fractalclockwork/core-memory/kicad/core_element_sim/models/array64x64_cycle_tb.cir

* Diagonal addressing smoke on the NxN MCE weave.
* Pin order matches magnetic_core_64x64.kicad_sch after Sim.Pins.
* Lines are 0-based: X0/Y0, X1/Y1, ... X63/Y63. There is no X64.
* This deck pulses X0/Y0 through X31/Y31.
*
* One CCS each for X, Y, and inhibit, 400 mA. Inhibit stays off.
* Each pulsed core gets one write 1 (1 us rise, 2 us flat, 1 us fall).
* The diagonal and one X half-select neighbor per address are the mce
* devices. Other positions are omitted; each driven line still
* series-connects the cores that sit on it. Sense is the early flat.
*
* Batch: kicad/core_element_sim/models/array64x64_cycle.sh
* Prints RESULT PASS or RESULT FAIL.

.include coremem.cir
.include ccs.cir

.param vdrive=12

Vdrive vdrv 0 DC {vdrive}
Viccsx ccs_x ccs_xin 0
Viccsy ccs_y ccs_yin 0
Viccsi ccs_i ccs_iin 0
Xccs_x ccs_xin ccs ic_half=0.4
Xccs_y ccs_yin ccs ic_half=0.4
Xccs_i ccs_iin ccs ic_half=0.4
Rx ccs_x 0 10Meg
Ry ccs_y 0 10Meg
Ri ccs_i 0 10Meg
Rfold FOLD 0 10k

Rxa0 xa0d 0 10Meg
Rya0 ya0d 0 10Meg
Rxa1 xa1d 0 10Meg
Rya1 ya1d 0 10Meg
Rxa2 xa2d 0 10Meg
Rya2 ya2d 0 10Meg
Rxa3 xa3d 0 10Meg
Rya3 ya3d 0 10Meg
Rxa4 xa4d 0 10Meg
Rya4 ya4d 0 10Meg
Rxa5 xa5d 0 10Meg
Rya5 ya5d 0 10Meg
Rxa6 xa6d 0 10Meg
Rya6 ya6d 0 10Meg
Rxa7 xa7d 0 10Meg
Rya7 ya7d 0 10Meg
Rxa8 xa8d 0 10Meg
Rya8 ya8d 0 10Meg
Rxa9 xa9d 0 10Meg
Rya9 ya9d 0 10Meg
Rxa10 xa10d 0 10Meg
Rya10 ya10d 0 10Meg
Rxa11 xa11d 0 10Meg
Rya11 ya11d 0 10Meg
Rxa12 xa12d 0 10Meg
Rya12 ya12d 0 10Meg
Rxa13 xa13d 0 10Meg
Rya13 ya13d 0 10Meg
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
Xr48c47 nx47_47 XB47 ny47_48 YB48 nyb47 nyb46 mce m0=-1
Xr48c48 XA48 nx48_48 YA48 ny47_48 nya15 nya14 mce m0=-1
Xr49c48 nx48_48 XB48 ny48_49 YB49 nyb48 nyb47 mce m0=-1
Xr49c49 XA49 nx49_49 YA49 ny48_49 nya14 nya13 mce m0=-1
Xr50c49 nx49_49 XB49 ny49_50 YB50 nyb49 nyb48 mce m0=-1
Xr50c50 XA50 nx50_50 YA50 ny49_50 nya13 nya12 mce m0=-1
Xr51c50 nx50_50 XB50 ny50_51 YB51 nyb50 nyb49 mce m0=-1
Xr51c51 XA51 nx51_51 YA51 ny50_51 nya12 nya11 mce m0=-1
Xr52c51 nx51_51 XB51 ny51_52 YB52 nyb51 nyb50 mce m0=-1
Xr52c52 XA52 nx52_52 YA52 ny51_52 nya11 nya10 mce m0=-1
Xr53c52 nx52_52 XB52 ny52_53 YB53 nyb52 nyb51 mce m0=-1
Xr53c53 XA53 nx53_53 YA53 ny52_53 nya10 nya9 mce m0=-1
Xr54c53 nx53_53 XB53 ny53_54 YB54 nyb53 nyb52 mce m0=-1
Xr54c54 XA54 nx54_54 YA54 ny53_54 nya9 nya8 mce m0=-1
Xr55c54 nx54_54 XB54 ny54_55 YB55 nyb54 nyb53 mce m0=-1
Xr55c55 XA55 nx55_55 YA55 ny54_55 nya8 nya7 mce m0=-1
Xr56c55 nx55_55 XB55 ny55_56 YB56 nyb55 nyb54 mce m0=-1
Xr56c56 XA56 nx56_56 YA56 ny55_56 nya7 nya6 mce m0=-1
Xr57c56 nx56_56 XB56 ny56_57 YB57 nyb56 nyb55 mce m0=-1
Xr57c57 XA57 nx57_57 YA57 ny56_57 nya6 nya5 mce m0=-1
Xr58c57 nx57_57 XB57 ny57_58 YB58 nyb57 nyb56 mce m0=-1
Xr58c58 XA58 nx58_58 YA58 ny57_58 nya5 nya4 mce m0=-1
Xr59c58 nx58_58 XB58 ny58_59 YB59 nyb58 nyb57 mce m0=-1
Xr59c59 XA59 nx59_59 YA59 ny58_59 nya4 nya3 mce m0=-1
Xr60c59 nx59_59 XB59 ny59_60 YB60 nyb59 nyb58 mce m0=-1
Xr60c60 XA60 nx60_60 YA60 ny59_60 nya3 nya2 mce m0=-1
Xr61c60 nx60_60 XB60 ny60_61 YB61 nyb60 nyb59 mce m0=-1
Xr61c61 XA61 nx61_61 YA61 ny60_61 nya2 nya1 mce m0=-1
Xr62c61 nx61_61 XB61 ny61_62 YB62 nyb61 nyb60 mce m0=-1
Xr62c62 XA62 nx62_62 ny62_62 ny61_62 nya1 nya0 mce m0=-1
Xr62c63 XA63 nx63_62 YA62 ny62_62 YB66 nyb62 mce m0=-1
Xr63c62 nx62_62 XB62 ny62_63 YB63 nyb62 nyb61 mce m0=-1
Xr63c63 nx63_62 XB63 YA63 ny62_63 nya0 YA65 mce m0=-1

Bdiff DIFF 0 V = V(YA65)-V(YB66)
Vinh inhd YA65 0
Bpinh PINH 0 V = I(Vinh)
Vixa0 xa0d XA0 0
Viya0 ya0d YA0 0
Bpxa0 PXA0 0 V = I(Vixa0)
Bpya0 PYA0 0 V = I(Viya0)
Vixa1 xa1d XA1 0
Viya1 ya1d YA1 0
Bpxa1 PXA1 0 V = I(Vixa1)
Bpya1 PYA1 0 V = I(Viya1)
Vixa2 xa2d XA2 0
Viya2 ya2d YA2 0
Bpxa2 PXA2 0 V = I(Vixa2)
Bpya2 PYA2 0 V = I(Viya2)
Vixa3 xa3d XA3 0
Viya3 ya3d YA3 0
Bpxa3 PXA3 0 V = I(Vixa3)
Bpya3 PYA3 0 V = I(Viya3)
Vixa4 xa4d XA4 0
Viya4 ya4d YA4 0
Bpxa4 PXA4 0 V = I(Vixa4)
Bpya4 PYA4 0 V = I(Viya4)
Vixa5 xa5d XA5 0
Viya5 ya5d YA5 0
Bpxa5 PXA5 0 V = I(Vixa5)
Bpya5 PYA5 0 V = I(Viya5)
Vixa6 xa6d XA6 0
Viya6 ya6d YA6 0
Bpxa6 PXA6 0 V = I(Vixa6)
Bpya6 PYA6 0 V = I(Viya6)
Vixa7 xa7d XA7 0
Viya7 ya7d YA7 0
Bpxa7 PXA7 0 V = I(Vixa7)
Bpya7 PYA7 0 V = I(Viya7)
Vixa8 xa8d XA8 0
Viya8 ya8d YA8 0
Bpxa8 PXA8 0 V = I(Vixa8)
Bpya8 PYA8 0 V = I(Viya8)
Vixa9 xa9d XA9 0
Viya9 ya9d YA9 0
Bpxa9 PXA9 0 V = I(Vixa9)
Bpya9 PYA9 0 V = I(Viya9)
Vixa10 xa10d XA10 0
Viya10 ya10d YA10 0
Bpxa10 PXA10 0 V = I(Vixa10)
Bpya10 PYA10 0 V = I(Viya10)
Vixa11 xa11d XA11 0
Viya11 ya11d YA11 0
Bpxa11 PXA11 0 V = I(Vixa11)
Bpya11 PYA11 0 V = I(Viya11)
Vixa12 xa12d XA12 0
Viya12 ya12d YA12 0
Bpxa12 PXA12 0 V = I(Vixa12)
Bpya12 PYA12 0 V = I(Viya12)
Vixa13 xa13d XA13 0
Viya13 ya13d YA13 0
Bpxa13 PXA13 0 V = I(Vixa13)
Bpya13 PYA13 0 V = I(Viya13)
Vixa14 xa14d XA14 0
Viya14 ya14d YA14 0
Bpxa14 PXA14 0 V = I(Vixa14)
Bpya14 PYA14 0 V = I(Viya14)
Vixa15 xa15d XA15 0
Viya15 ya15d YA15 0
Bpxa15 PXA15 0 V = I(Vixa15)
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
Bpxa58 PXA58 0 V = I(Vixa58)
Bpya58 PYA58 0 V = I(Viya58)
Vixa59 xa59d XA59 0
Viya59 ya59d YA59 0
Bpxa59 PXA59 0 V = I(Vixa59)
Bpya59 PYA59 0 V = I(Viya59)
Vixa60 xa60d XA60 0
Viya60 ya60d YA60 0
Bpxa60 PXA60 0 V = I(Vixa60)
Bpya60 PYA60 0 V = I(Viya60)
Vixa61 xa61d XA61 0
Viya61 ya61d YA61 0
Bpxa61 PXA61 0 V = I(Vixa61)
Bpya61 PYA61 0 V = I(Viya61)
Vixa62 xa62d XA62 0
Viya62 ya62d YA62 0
Bpxa62 PXA62 0 V = I(Vixa62)
Bpya62 PYA62 0 V = I(Viya62)
Vixa63 xa63d XA63 0
Viya63 ya63d YA63 0
Bpxa63 PXA63 0 V = I(Vixa63)
Bpya63 PYA63 0 V = I(Viya63)

* Ramps from a few hundred ohms down to 1 ohm across the 1 us edge.
.subckt drvsw a b ctl
Bsw a b I=(v(ctl)>0.02 ? v(a,b)/(1+400*(1-min(v(ctl),1))) : 0)
.ends
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
