fractalclockwork/core-memory/kicad/core_element_sim/models/array64x64_ideal_tb.cir

* L3 idealized diagonal addressing smoke (ideal_mce).
* One continuous transient: write-1 on X0/Y0 .. X63/Y63.
* Three CCS copies at 400 mA. Ideal drvsw. Inhibit off.
* Sparse plant: diagonal + one X half-select neighbor per address.
* Prints RESULT PASS or RESULT FAIL.

.include ideal_core.cir
.include ccs.cir

.param vdrive=12

Vdrive vdrv 0 DC {vdrive}
Viccsx ccs_x ccs_xin 0
Viccsy ccs_y ccs_yin 0
Viccsi ccs_i ccs_iin 0
Xccs_x ccs_xin ccs ic_half=0.4
Xccs_y ccs_yin ccs ic_half=0.4
Xccs_i ccs_iin ccs ic_half=0.4
Rx ccs_x 0 10Meg
Ry ccs_y 0 10Meg
Ri ccs_i 0 10Meg
Rfold FOLD 0 10k

Rxa0 xa0d 0 10Meg
Rya0 ya0d 0 10Meg
Rxa1 xa1d 0 10Meg
Rya1 ya1d 0 10Meg
Rxa2 xa2d 0 10Meg
Rya2 ya2d 0 10Meg
Rxa3 xa3d 0 10Meg
Rya3 ya3d 0 10Meg
Rxa4 xa4d 0 10Meg
Rya4 ya4d 0 10Meg
Rxa5 xa5d 0 10Meg
Rya5 ya5d 0 10Meg
Rxa6 xa6d 0 10Meg
Rya6 ya6d 0 10Meg
Rxa7 xa7d 0 10Meg
Rya7 ya7d 0 10Meg
Rxa8 xa8d 0 10Meg
Rya8 ya8d 0 10Meg
Rxa9 xa9d 0 10Meg
Rya9 ya9d 0 10Meg
Rxa10 xa10d 0 10Meg
Rya10 ya10d 0 10Meg
Rxa11 xa11d 0 10Meg
Rya11 ya11d 0 10Meg
Rxa12 xa12d 0 10Meg
Rya12 ya12d 0 10Meg
Rxa13 xa13d 0 10Meg
Rya13 ya13d 0 10Meg
Rxa14 xa14d 0 10Meg
Rya14 ya14d 0 10Meg
Rxa15 xa15d 0 10Meg
Rya15 ya15d 0 10Meg
Rxa16 xa16d 0 10Meg
Rya16 ya16d 0 10Meg
Rxa17 xa17d 0 10Meg
Rya17 ya17d 0 10Meg
Rxa18 xa18d 0 10Meg
Rya18 ya18d 0 10Meg
Rxa19 xa19d 0 10Meg
Rya19 ya19d 0 10Meg
Rxa20 xa20d 0 10Meg
Rya20 ya20d 0 10Meg
Rxa21 xa21d 0 10Meg
Rya21 ya21d 0 10Meg
Rxa22 xa22d 0 10Meg
Rya22 ya22d 0 10Meg
Rxa23 xa23d 0 10Meg
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
Vg_x54r g_x54r 0 DC 0
Vg_y54r g_y54r 0 DC 0
Xx55_ra xa55d ccs_x g_x55r drvsw
Xx55_rb vdrv XB55 g_x55r drvsw
Xx55_wa vdrv xa55d g_x55w drvsw
Xx55_wb XB55 ccs_x g_x55w drvsw
Xy55_ra ya55d ccs_y g_y55r drvsw
Xy55_rb vdrv YB55 g_y55r drvsw
Xy55_wa vdrv ya55d g_y55w drvsw
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
