fractalclockwork/core-memory/kicad/core_element_sim/models/array2x2_inhibit_tb.cir

* 2x2 matrix with the inhibit sheet (inhibit.cir) on CCS_INH.
* Same weave and Sim.Pins map as array2x2_tb.cir.
*
* One CCS for the X lines, one for the Y lines, one for inhibit, each 400 mA.
* Only one line on an axis is driven at a time, so that axis sink is the
* full half-select. All four cores start at m=-1.
*
* X00  X0/Y0  2 write 1, 8 read 1, 14 write-back 1, 20 clear, 26 write 0, 32 read 0, 38 write-back 0
* X01  X1/Y0  44 write 1, 50 read 1, 56 write-back 1, 62 clear, 68 write 0, 74 read 0, 80 write-back 0
* X10  X0/Y1  86 write 1, 92 read 1, 98 write-back 1, 104 clear, 110 write 0, 116 read 0, 122 write-back 0
* X11  X1/Y1  128 write 1, 134 read 1, 140 write-back 1, 146 clear, 152 write 0, 158 read 0, 164 write-back 0
*
* 1 us edges, 2 us flat, 1 us fall. Read sinks the A end (B->A).
* Write sinks the B end. Inhibit sources YA65 and sinks YB66.
* VDRIVE = 12 V is testbench headroom, not a frozen rail.
*
* Positive probe current is A->B. Batch: ngspice -b array2x2_matrix_tb.cir
* Prints RESULT PASS or RESULT FAIL.

.include coremem.cir
.include ccs.cir
.include drive.cir
.include inhibit.cir

.param vdrive=12

Vdrive vdrv 0 DC {vdrive}
Viccsx ccs_x ccs_xin 0
Viccsy ccs_y ccs_yin 0
Viccsi ccs_i ccs_iin 0
Xccs_x ccs_xin ccs ic_half=0.4
Xccs_y ccs_yin ccs ic_half=0.4
Xccs_i ccs_iin ccs ic_half=0.4
Rx ccs_x 0 10Meg
Ry ccs_y 0 10Meg
Ri ccs_i 0 10Meg

Rxa0 xa0d 0 10Meg
Rxa1 xa1d 0 10Meg
Rya0 ya0d 0 10Meg
Rya1 ya1d 0 10Meg
Rfold FOLD 0 10k

* X1 X2 Y1 Y2 S1 S2
X00 XA0 nX0 nY0 YB0 FOLD nSA mce m0=-1
X10 nX0 XB0 nY1 YB1 nSB FOLD mce m0=-1
X01 XA1 nX1 YA0 nY0 YB66 nSB mce m0=-1
X11 nX1 XB1 YA1 nY1 nSA YA65 mce m0=-1

Bdiff DIFF 0 V = V(YA65)-V(YB66)

Vixa0 xa0d XA0 0
Vixa1 xa1d XA1 0
Viya0 ya0d YA0 0
Viya1 ya1d YA1 0
Vinh inhd YA65 0
Bpxa0 PXA0 0 V = I(Vixa0)
Bpxa1 PXA1 0 V = I(Vixa1)
Bpya0 PYA0 0 V = I(Viya0)
Bpya1 PYA1 0 V = I(Viya1)
Bpinh PINH 0 V = I(Vinh)
Bpiccsx PICCSX 0 V = I(Viccsx)
Bpiccsy PICCSY 0 V = I(Viccsy)
Bpiccsi PICCSI 0 V = I(Viccsi)

* Ramps from a few hundred ohms down to 1 ohm across the 1 us edge.
.subckt drvsw a b ctl
Bsw a b I=(v(ctl)>0.02 ? v(a,b)/(1+400*(1-min(v(ctl),1))) : 0)
.ends

* 200 ns on each gate. A raw PWL corner into both lines of a shared HS
* drops the trap step to the floor.
.subckt glag in out
R1 in out 2k
C1 out 0 100p
.ends
Xlx0r g_x0r gx0r glag
Xlx1r g_x1r gx1r glag
Xlx0w g_x0w gx0w glag
Xlx1w g_x1w gx1w glag
Xly0r g_y0r gy0r glag
Xly1r g_y1r gy1r glag
Xly0w g_y0w gy0w glag
Xly1w g_y1w gy1w glag
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
